ChladpavPy/ZeroPad-Macropad/Images/pcb_b.png

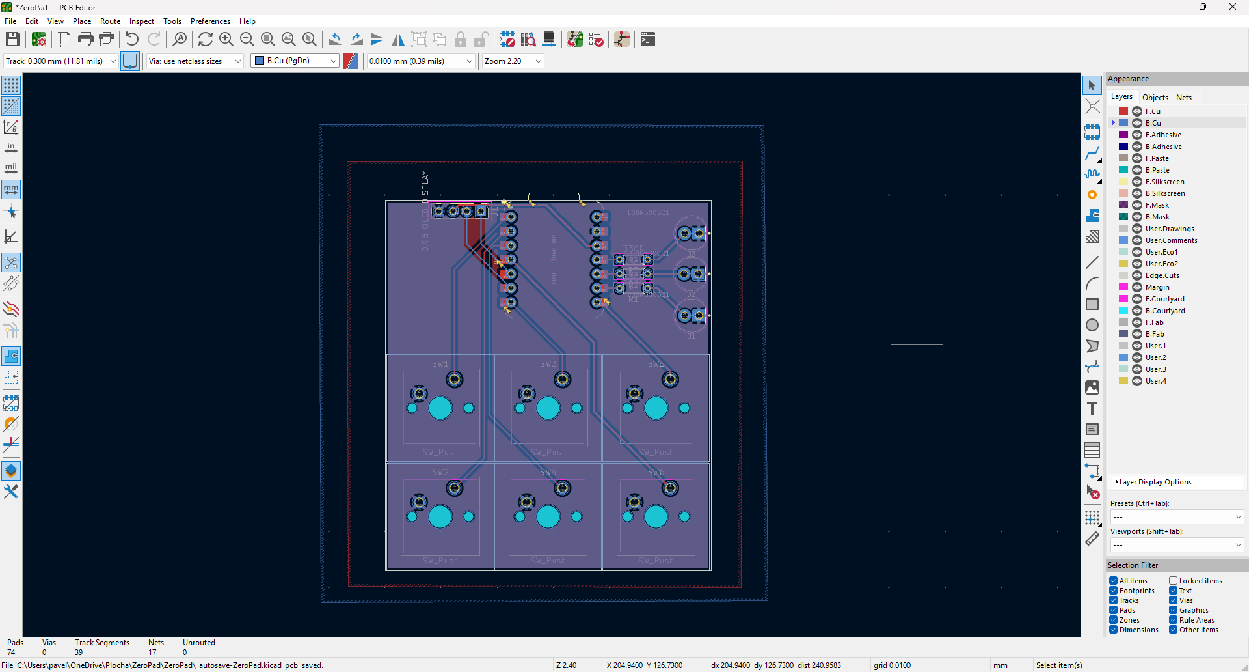
Images/pcb_b.png
